Han-ZenX/SIG_COND/docs/reference/scopefun/p2_term_L.png

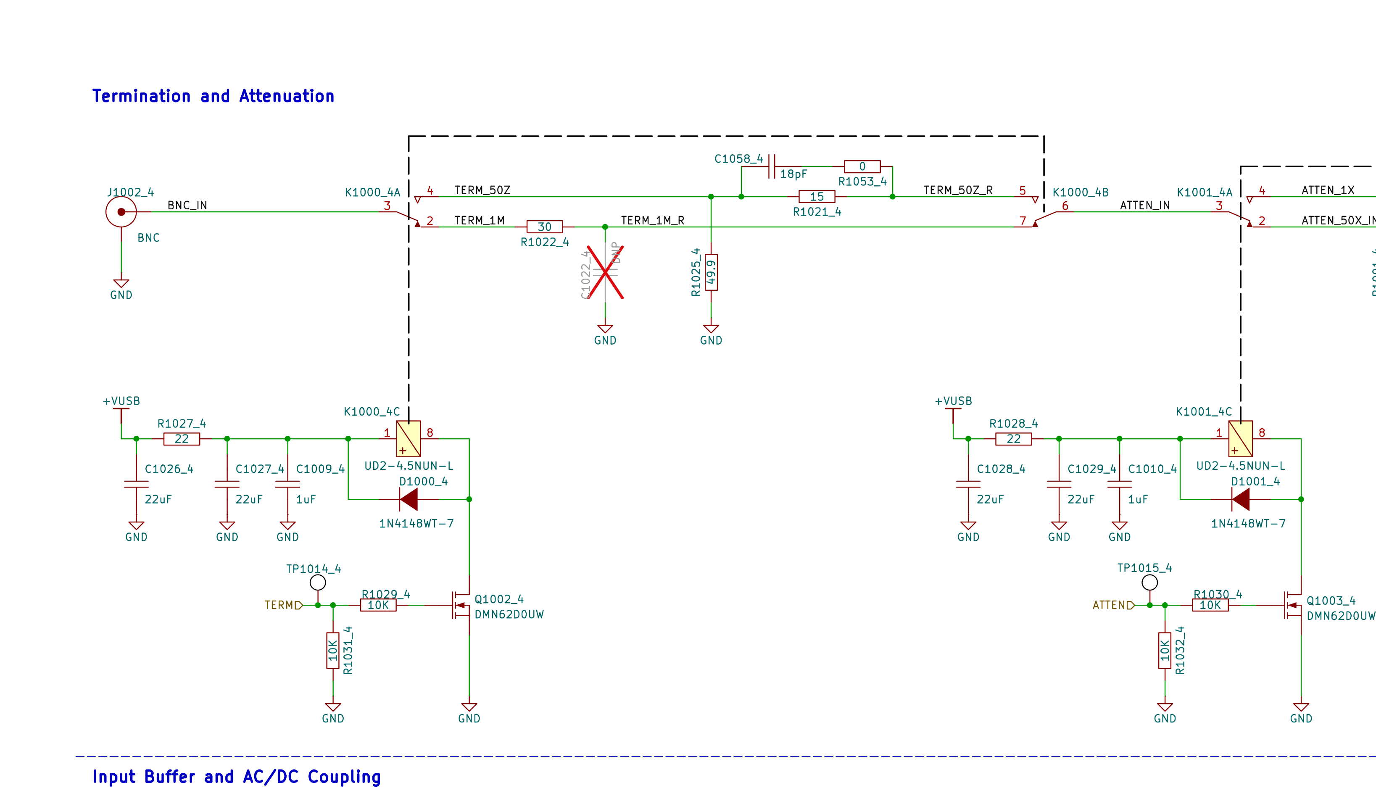
docs/reference/scopefun/p2_term_L.png
