Han-ZenX/SIG_COND/docs/reference/scopefun/p2_term_R.png

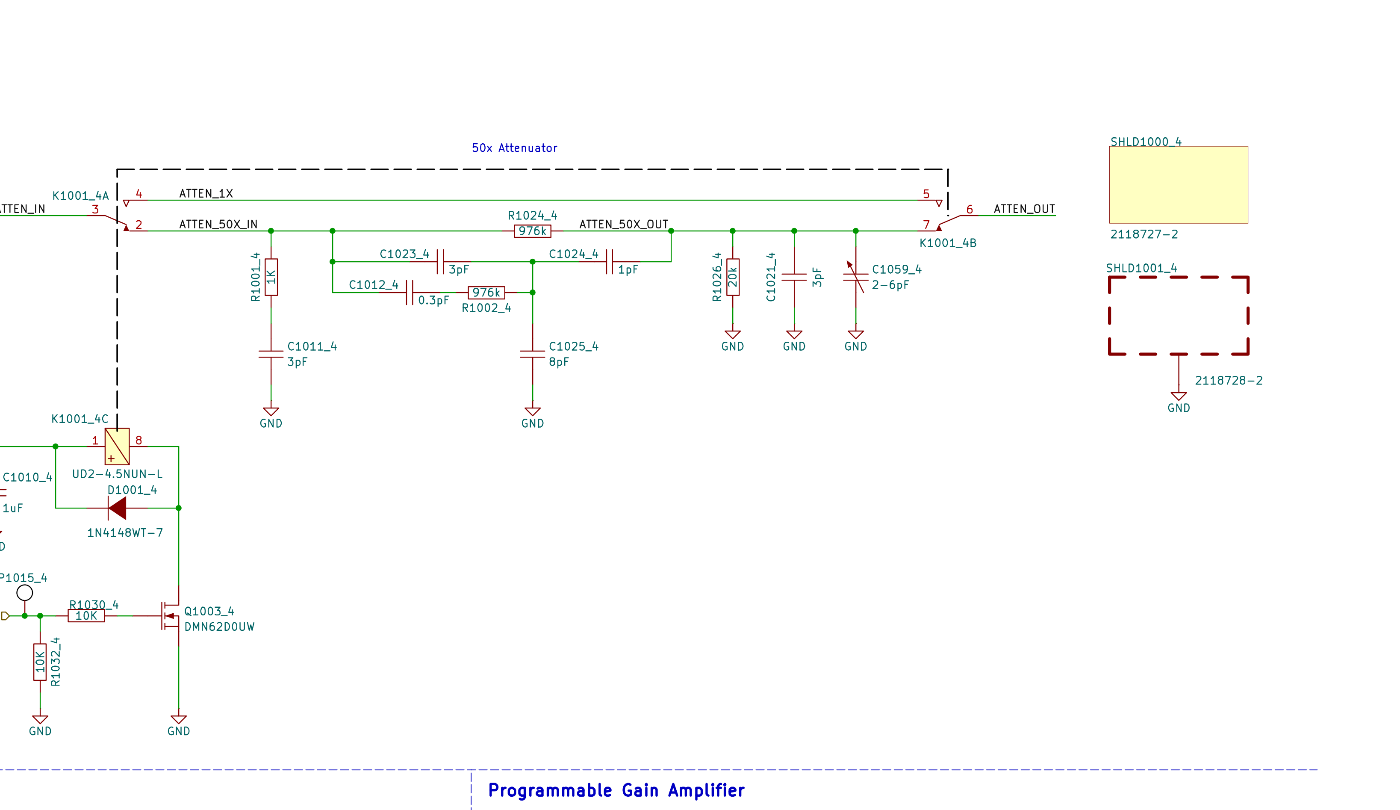
docs/reference/scopefun/p2_term_R.png
