Han-ZenX/SIG_COND/docs/reference/scopefun/p10_trim.png

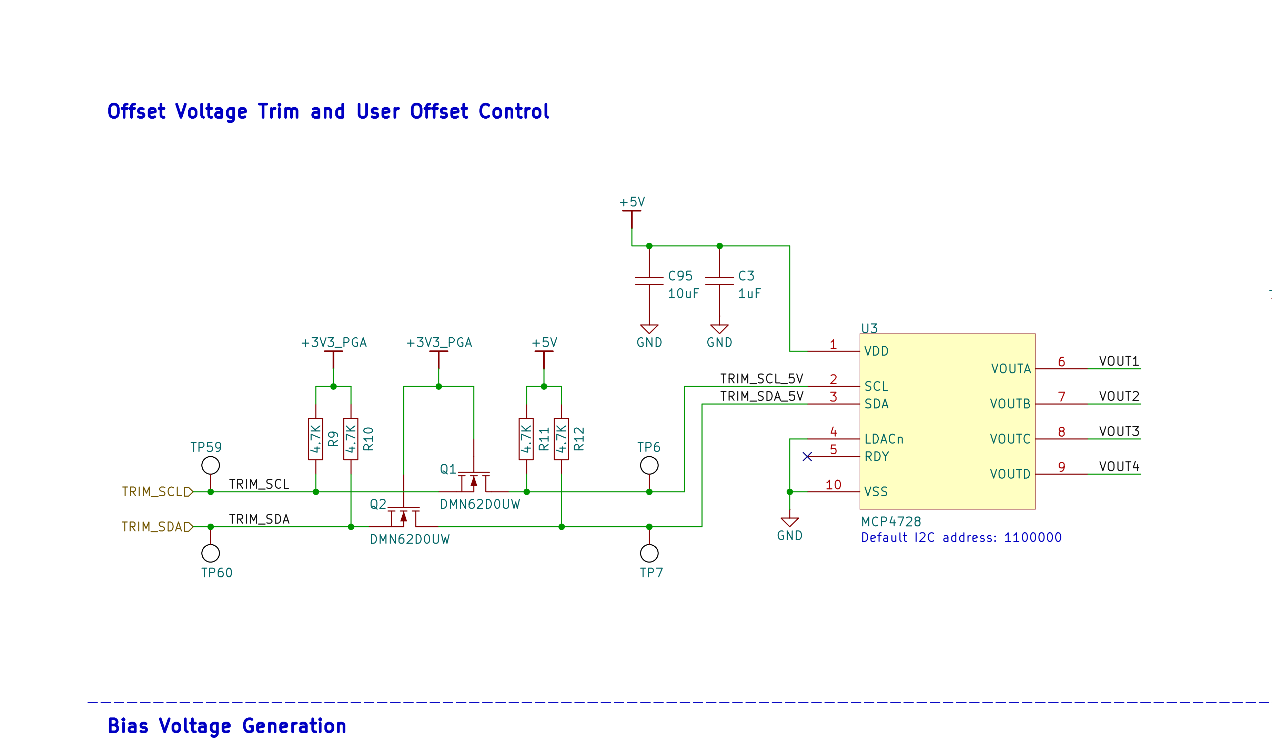
docs/reference/scopefun/p10_trim.png
