Han-ZenX/SIG_COND/docs/reference/scopefun/p13_fe_pwr.png

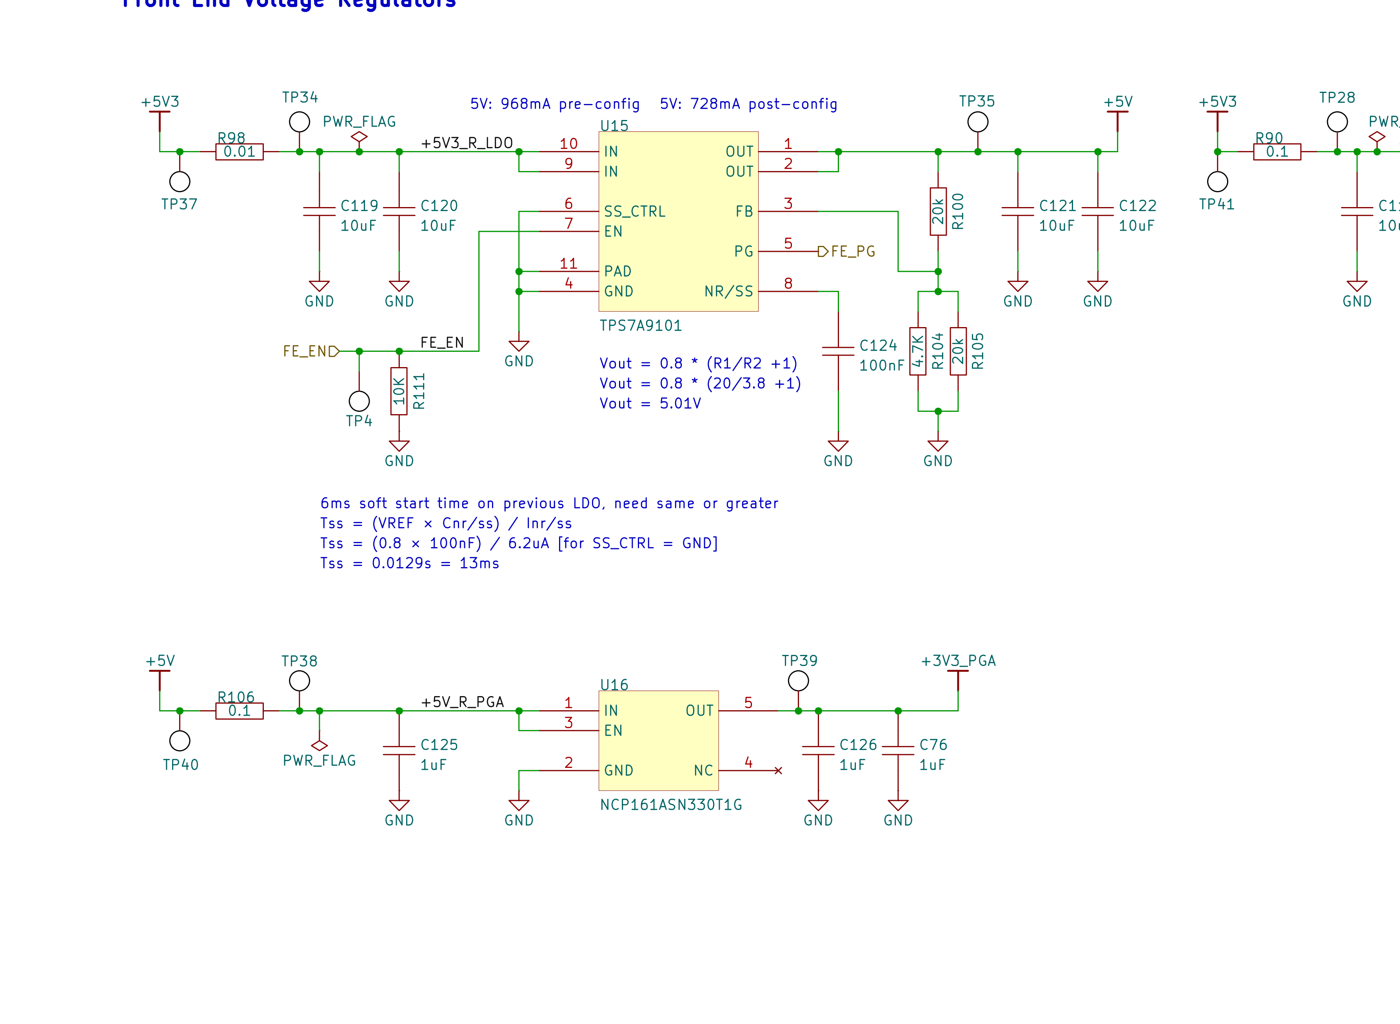
docs/reference/scopefun/p13_fe_pwr.png
