Han-ZenX/SIG_COND/docs/reference/scopefun/sheet.png

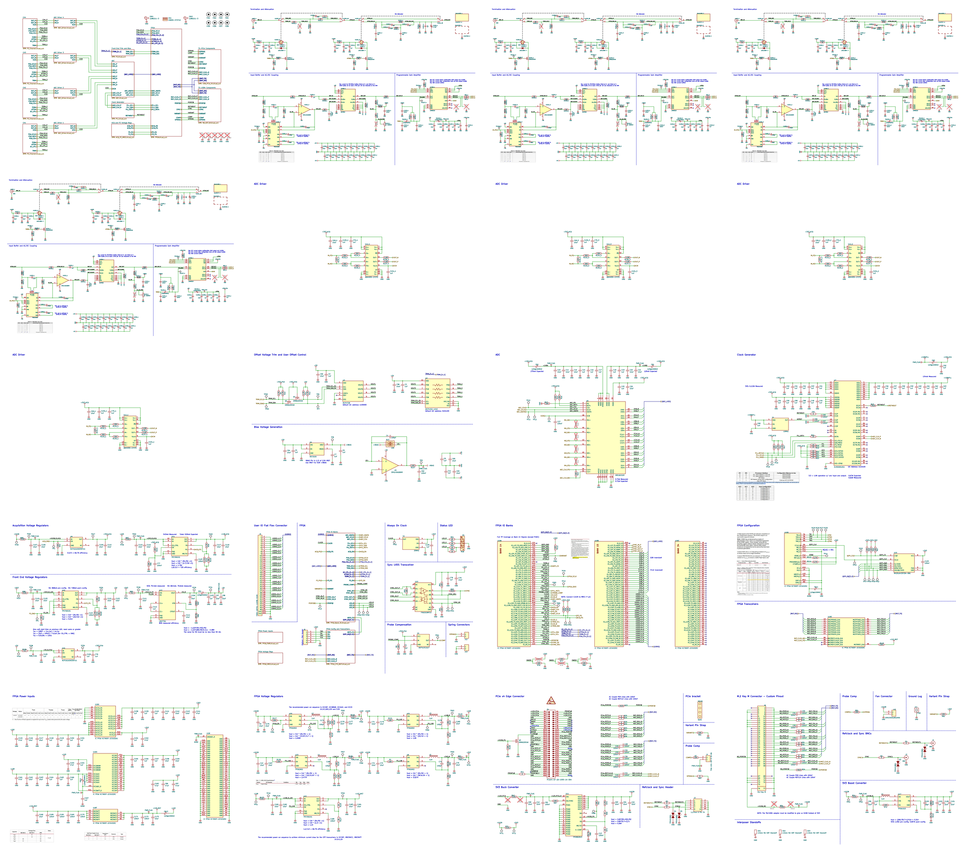
docs/reference/scopefun/sheet.png
