Han-ZenX/SIG_COND/hardware/schematic/v1.0/Thunderscope_Rev5.3/Outputs/TS-USB4 Assembly/Thunderscope_Rev5.3_TS_USB4_Schematic.pdf

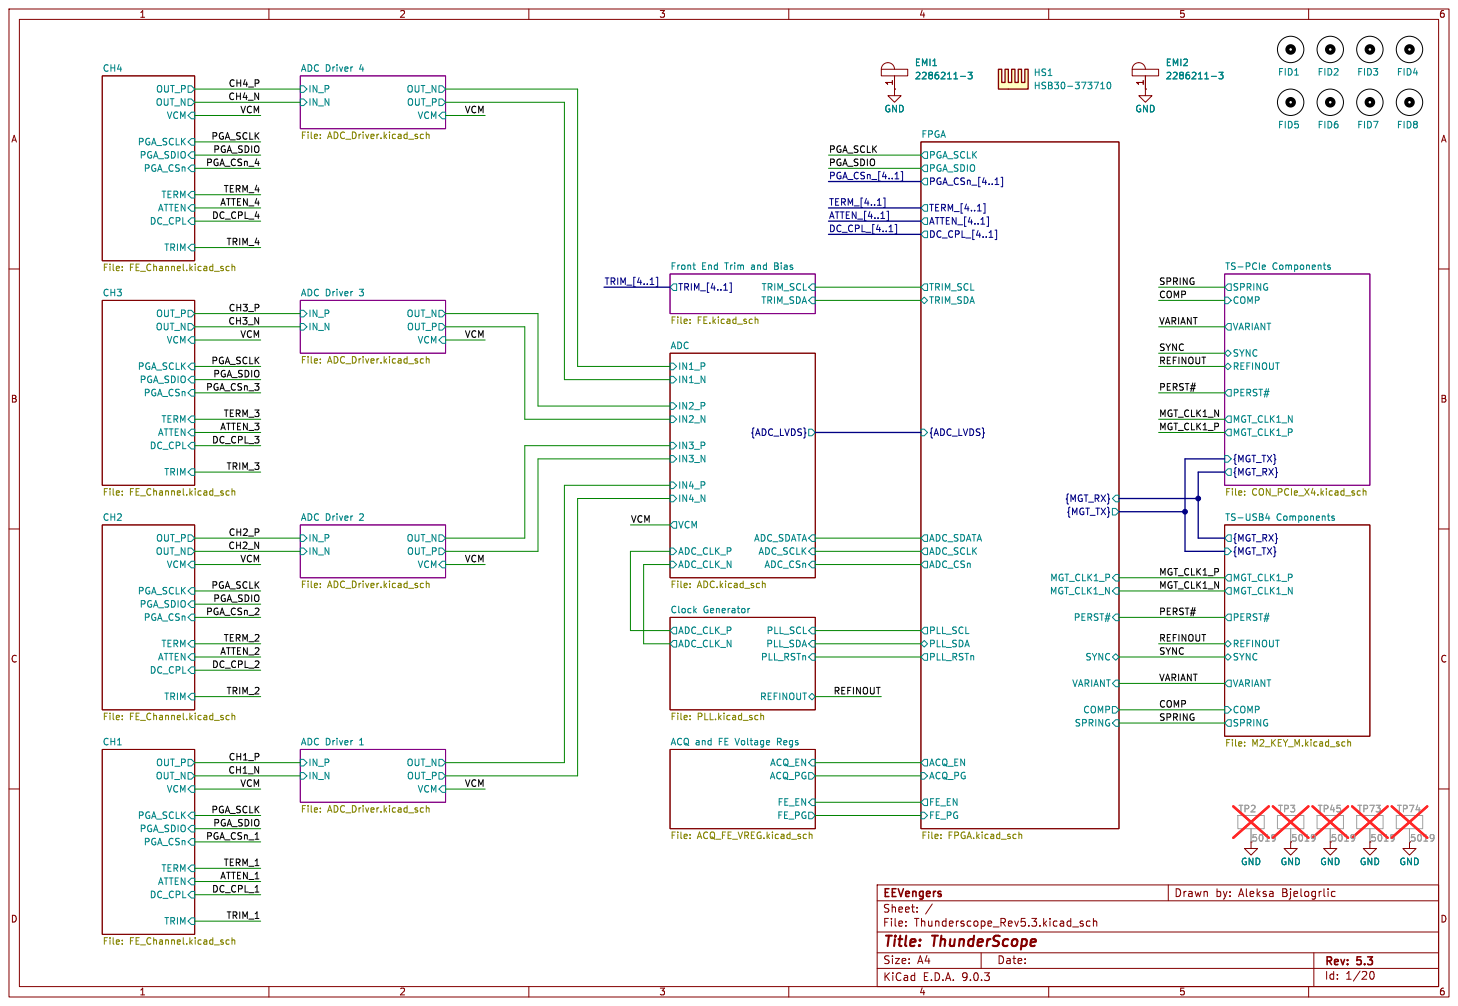
[picture p56: page 1]

TRIM_[4..1] Front End Trim and Bias File: FE.kicad_sch VCM

TS-USB4 Components File: M2_KEY_M.kicad_sch VCM

PLL_SCL REFINOUT Clock Generator File: PLL.kicad_sch

ACQ and FE Voltage Regs File: ACQ_FE_VREG.kicad_sch


Input Buffer and AC/DC Coupling

100k R_Bias wil be lower: 17mA per rail was measured on the EVM

This cap is switched in
during AC coupling This cap is switched in


Input Buffer and AC/DC Coupling

100k R_Bias wil be lower: 17mA per rail was measured on the EVM

This cap is switched in
during AC coupling This cap is switched in


Input Buffer and AC/DC Coupling

100k R_Bias wil be lower: 17mA per rail was measured on the EVM

This cap is switched in
during AC coupling This cap is switched in


Input Buffer and AC/DC Coupling

100k R_Bias wil be lower: 17mA per rail was measured on the EVM

This cap is switched in
during AC coupling This cap is switched in







1 AVSS2 31 AVDD 36 AVSS 39 AVDD2 32 AVSS 42 AVSS 45 DVDD 30 EPAD 49 DVDD

8 OVDD 33 DVSS 29 D4B- 28 D4B+ 27 D4A- 26 D4A+ 25 D3B- 24 D3B+ 23 D3A- 22 D3A+ 21 FCLK- 20 FCLK+ 19


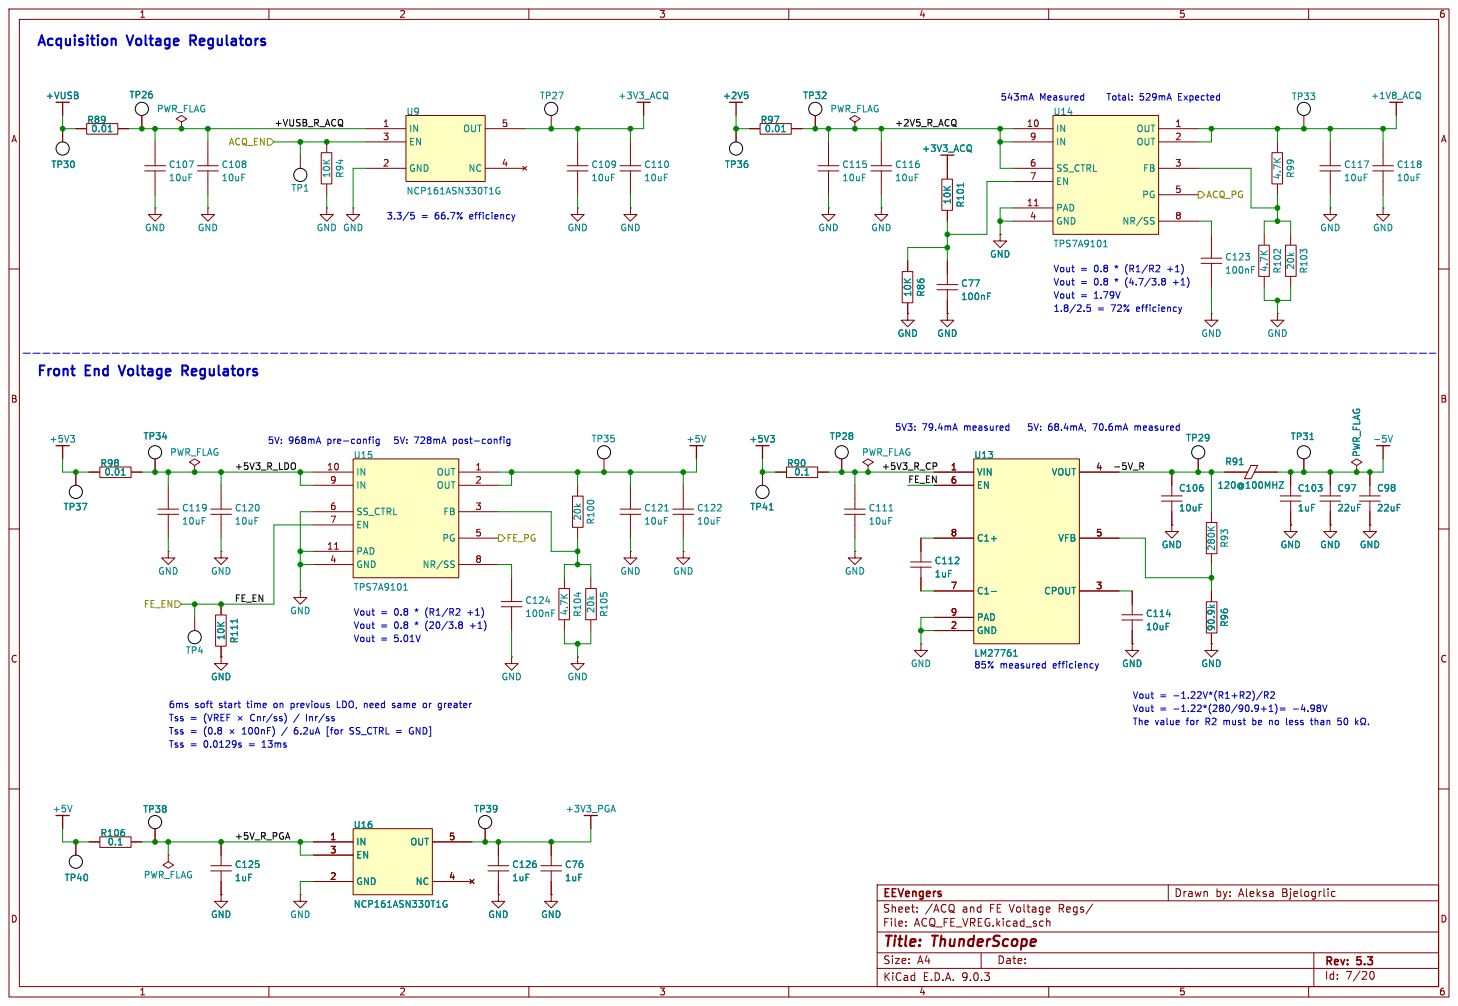
[picture p57: page 13]


FPGA IO Banks File: FPGA_Bank_IO.kicad_sch TDI TDO
{USRIO} SYNC_IN_P




NOTE: Connect CLK25 to MRCC P pin


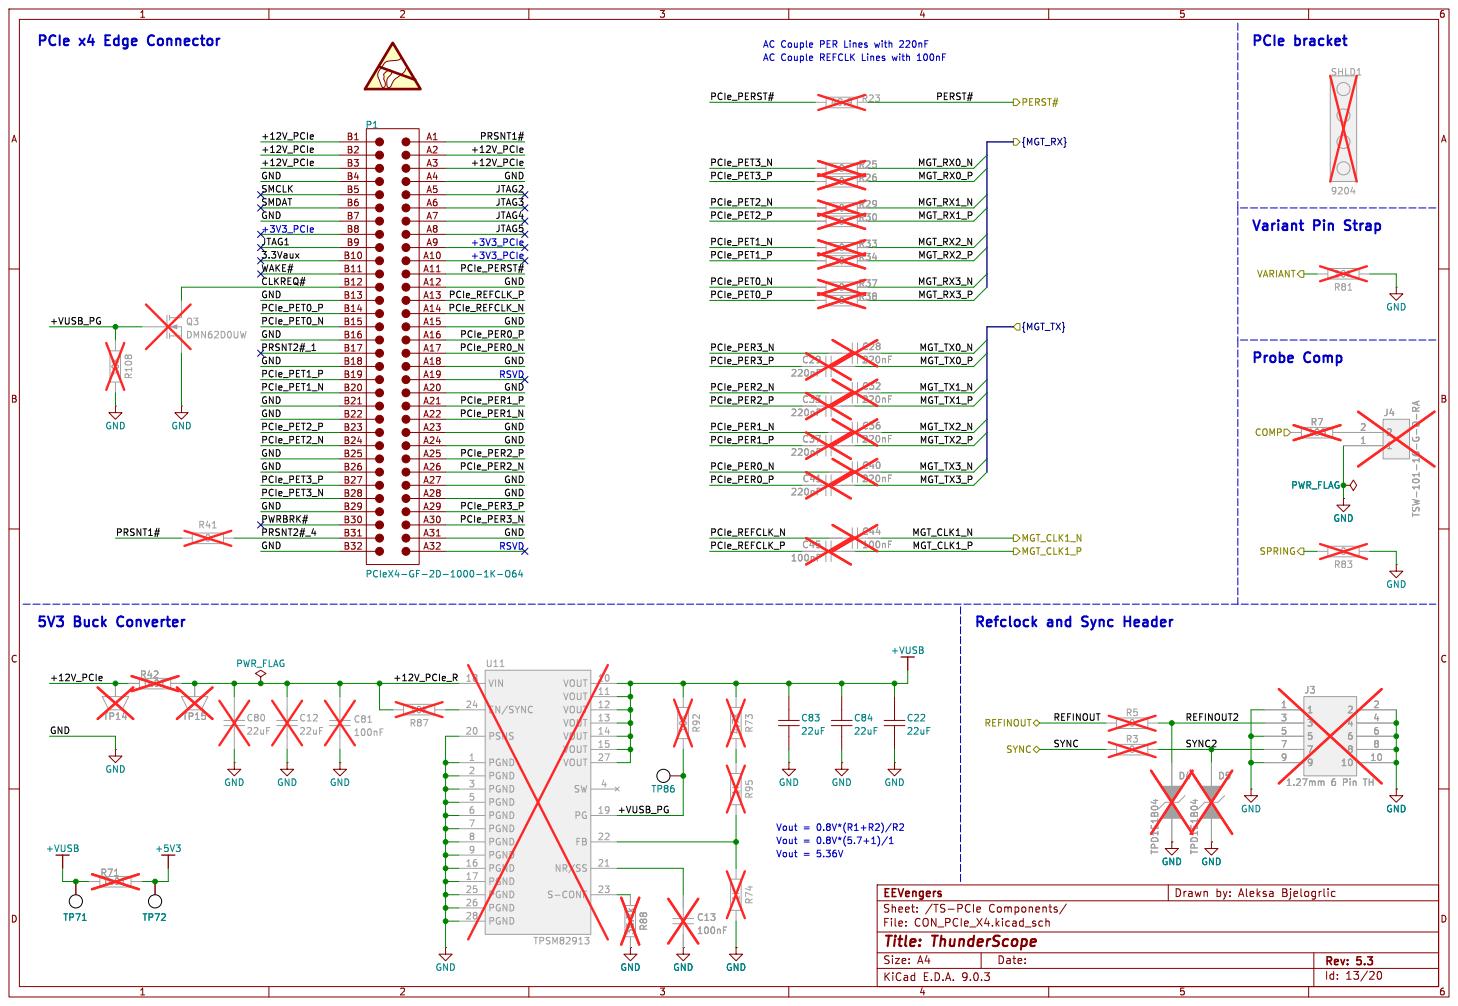
[picture p58: page 19]

AC Couple REFCLK Lines with 100nF

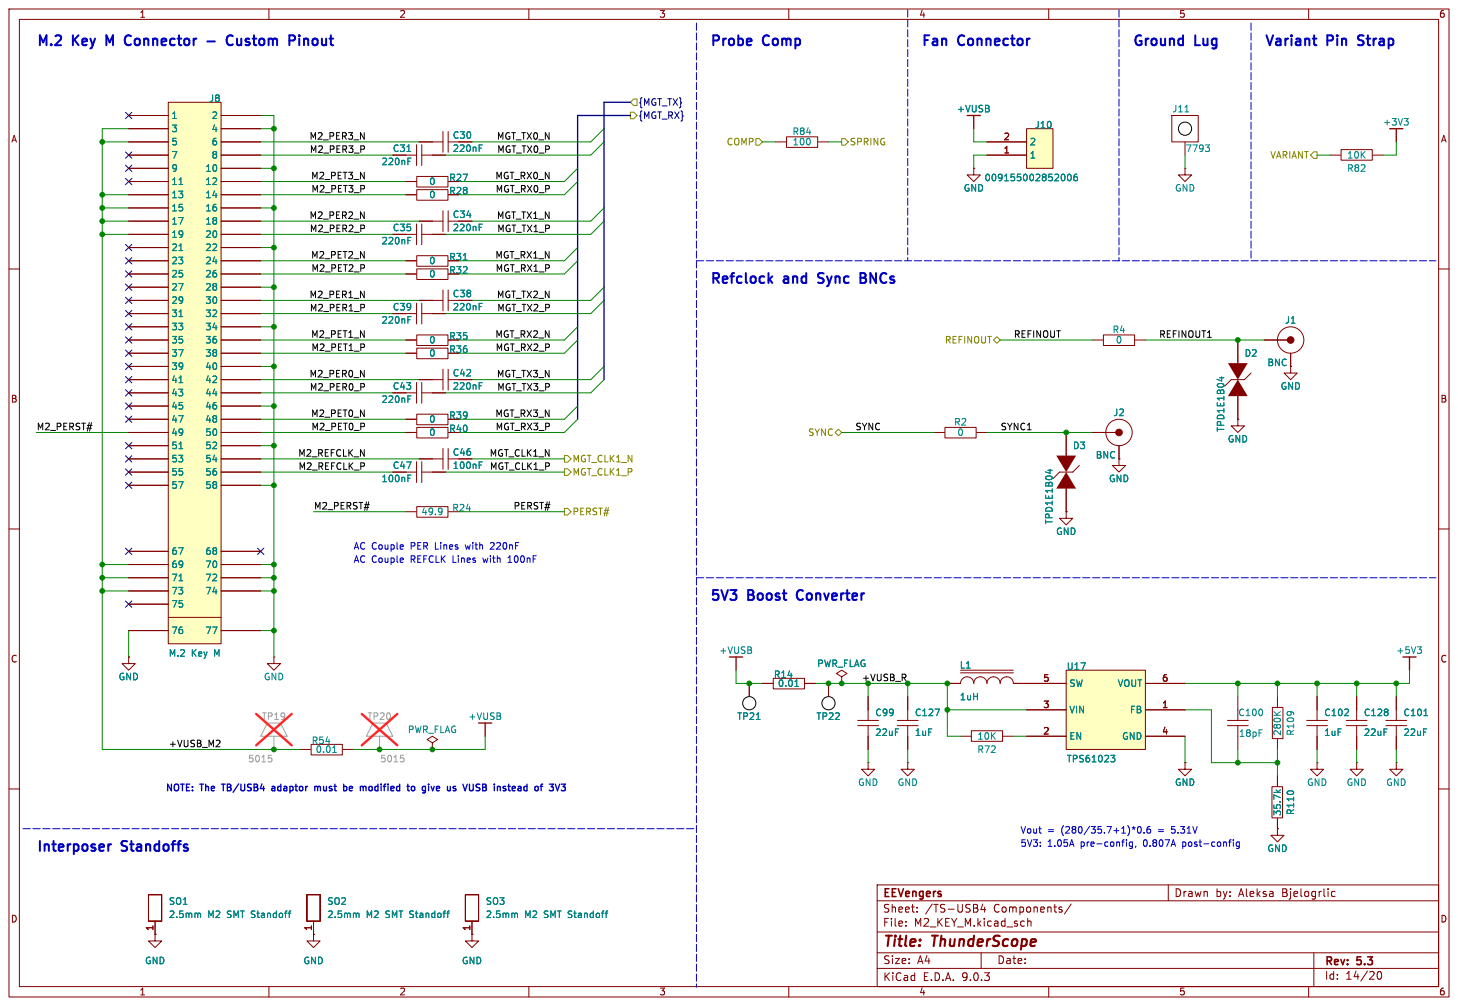
[picture p59: page 20]

Refclock and Sync BNCs
